rellpa/covitor_watch/Android Application/Demo App/Choose Device.jpg

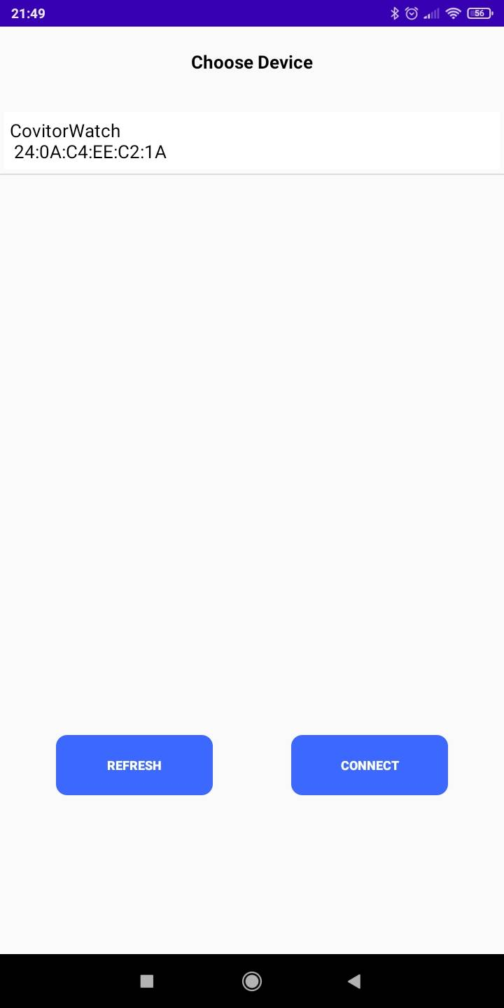
Android Application/Demo App/Choose Device.jpg
