rellpa/covitor_watch/Android Application/Demo App/Readings 4.jpg

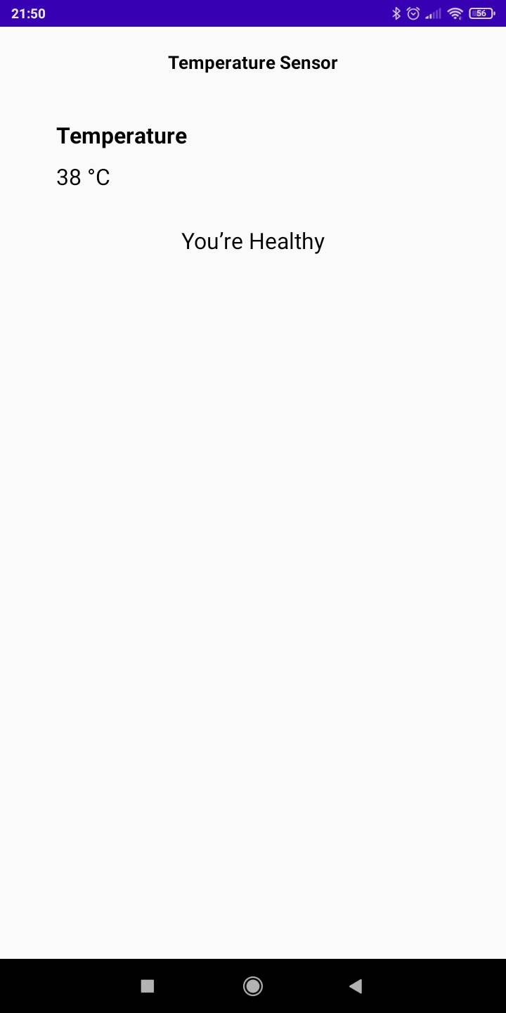
Android Application/Demo App/Readings 4.jpg
