rellpa/covitor_watch/Android Application/Demo App/Welcome Screen.jpg

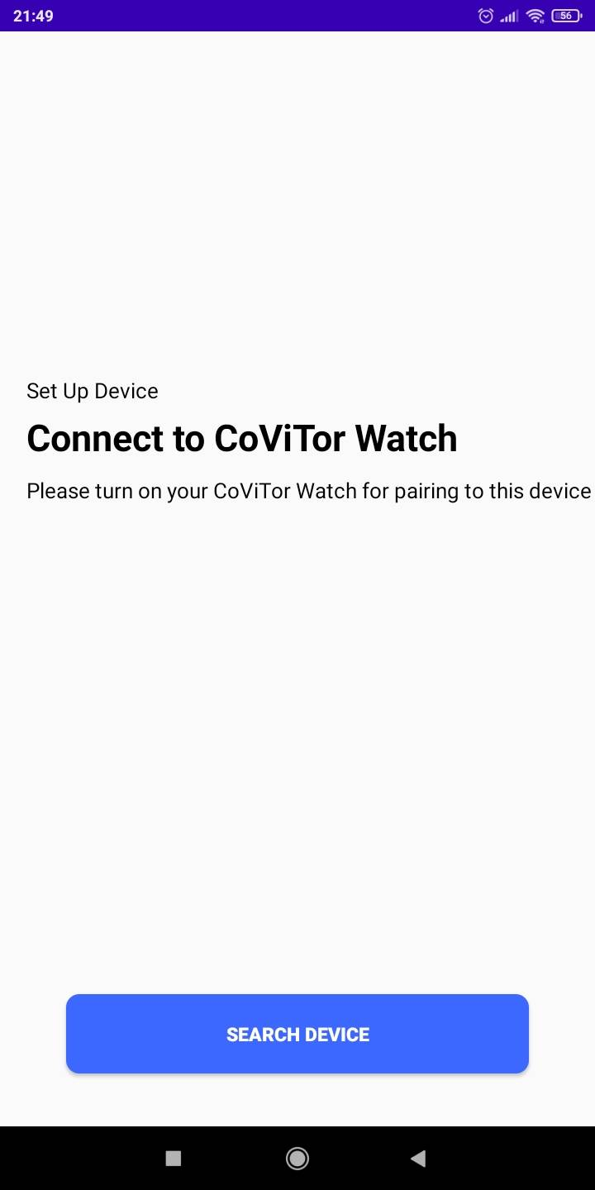
Android Application/Demo App/Welcome Screen.jpg
