rellpa/covitor_watch/Embedded System/Watch Enclosure/Enclosure 1.jpg

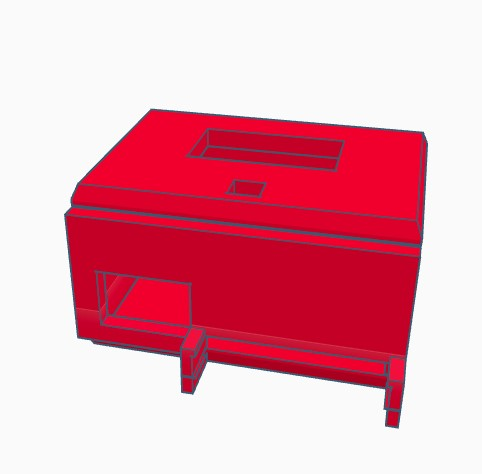
Embedded System/Watch Enclosure/Enclosure 1.jpg
