rellpa/covitor_watch/Embedded System/Watch Enclosure/Enclosure 2.jpg

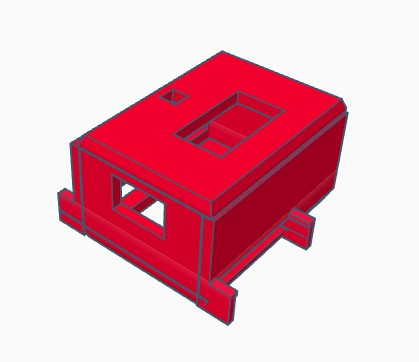
Embedded System/Watch Enclosure/Enclosure 2.jpg
