rellpa/covitor_watch/Embedded System/Watch Enclosure/Enclosure 3.jpg

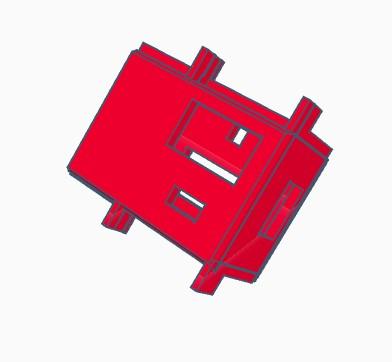
Embedded System/Watch Enclosure/Enclosure 3.jpg
